hwkim3330/pi5-joycon-handheld/out/acrylic/v7_clear_acrylzip/preview_slot.png

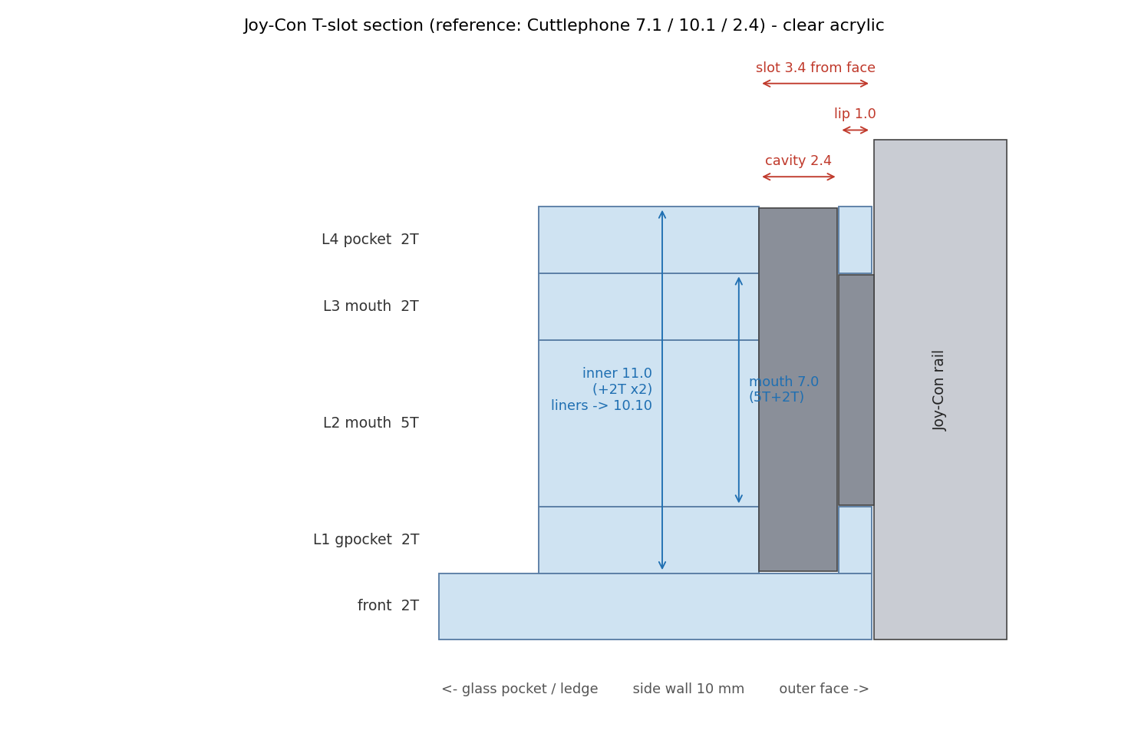
out/acrylic/v7_clear_acrylzip/preview_slot.png
