hwkim3330/pi5-joycon-handheld/out/acrylic/v8_clear_straightguide_ordered/sheet_2T.dxf

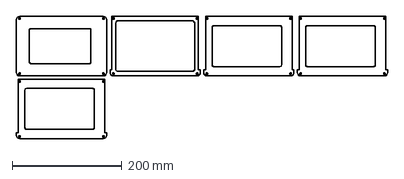
[picture p23: CAD file, 2026-09-11]
out/acrylic/v8_clear_straightguide_ordered/sheet_2T.dxf
675.6 x 222.9 mm
