hwkim3330/pi5-joycon-handheld/out/acrylic/v8r_liplayers_recut/L5r_pocket_lip_2T.dxf

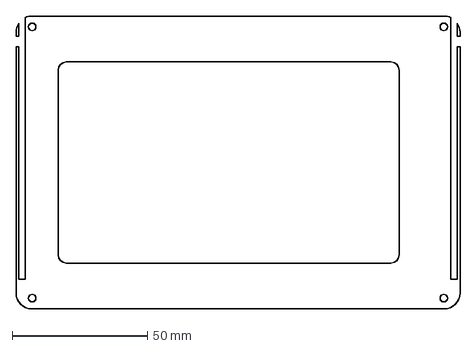
[picture p24: CAD file, 2026-09-11]
out/acrylic/v8r_liplayers_recut/L5r_pocket_lip_2T.dxf
164.4 x 108.5 mm
