hwkim3330/pi5-joycon-handheld/out/acrylic/test_coupon_exact/sheet_1.5T.dxf

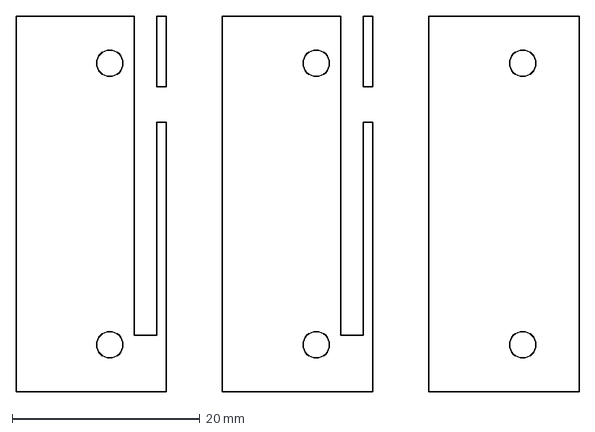
[picture p26: CAD file, 2026-09-11]
out/acrylic/test_coupon_exact/sheet_1.5T.dxf
60.0 x 40.0 mm
