hwkim3330/pi5-joycon-handheld/out/acrylic/v7_clear_acrylzip/sheet_2T.dxf

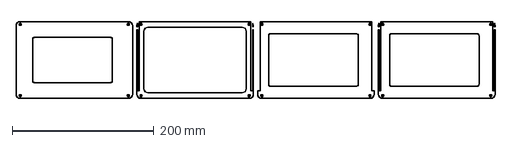
[picture p29: CAD file, 2026-09-11]
out/acrylic/v7_clear_acrylzip/sheet_2T.dxf
675.6 x 108.5 mm
