hwkim3330/pi5-joycon-handheld/out/acrylic/v8_clear_straightguide_ordered/L2_guide_3T.dxf

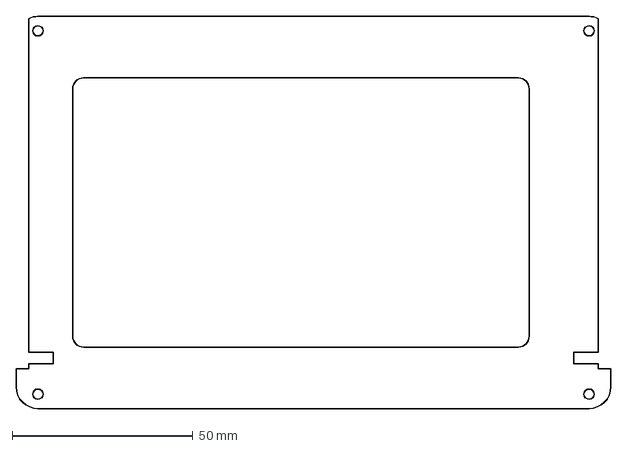
[picture p31: CAD file, 2026-09-11]
out/acrylic/v8_clear_straightguide_ordered/L2_guide_3T.dxf
164.4 x 108.5 mm
