hwkim3330/pi5-joycon-handheld/out/acrylic/test_coupon_acrylzip/sheet_2T.dxf

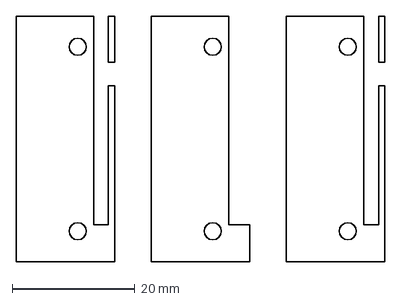
[picture p33: CAD file, 2026-09-11]
out/acrylic/test_coupon_acrylzip/sheet_2T.dxf
60.0 x 40.0 mm
