hwkim3330/pi5-joycon-handheld/out/acrylic/test_coupon_ordered/C2_guide_3T.dxf

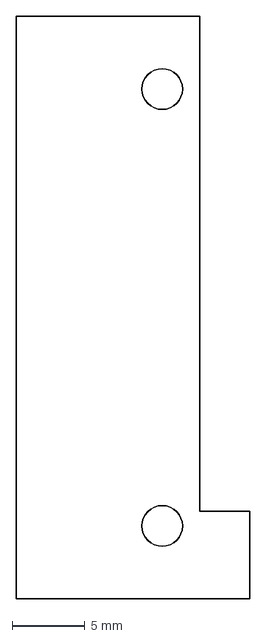
[picture p35: CAD file, 2026-09-11]
out/acrylic/test_coupon_ordered/C2_guide_3T.dxf
16.0 x 40.0 mm
