hwkim3330/pi5-joycon-handheld/out/acrylic/v4_open_back/sheet_3T.dxf

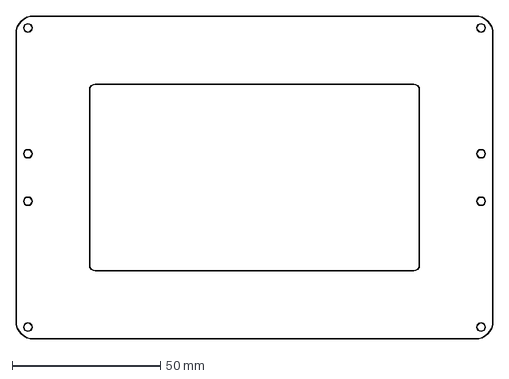
[picture p36: CAD file, 2026-09-08]
out/acrylic/v4_open_back/sheet_3T.dxf
161.0 x 109.0 mm
