hwkim3330/pi5-joycon-handheld/out/acrylic/v7_clear_exact/sheet_1.5T.dxf

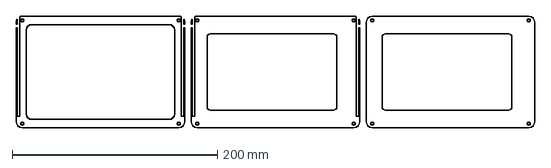
[picture p38: CAD file, 2026-09-11]
out/acrylic/v7_clear_exact/sheet_1.5T.dxf
505.2 x 108.5 mm
