hwkim3330/pi5-joycon-handheld/out/acrylic/test_coupon_exact/C4_pocket_1.5T.dxf

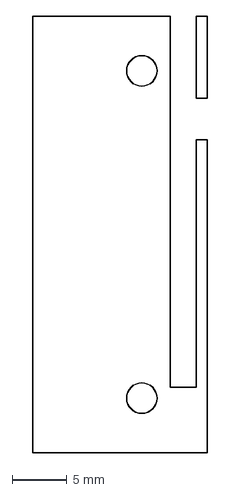
[picture p41: CAD file, 2026-09-11]
out/acrylic/test_coupon_exact/C4_pocket_1.5T.dxf
16.0 x 40.0 mm
