hwkim3330/pi5-joycon-handheld/out/acrylic/test_coupon_acrylzip/sheet_5T.dxf

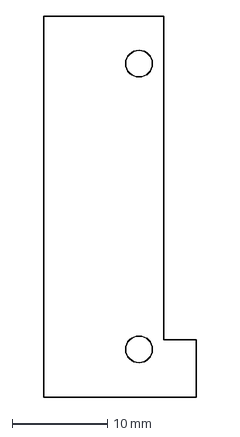
[picture p47: CAD file, 2026-09-11]
out/acrylic/test_coupon_acrylzip/sheet_5T.dxf
16.0 x 40.0 mm
