hwkim3330/pi5-joycon-handheld/out/acrylic/test_coupon_exact/C3_mouth_2T.dxf

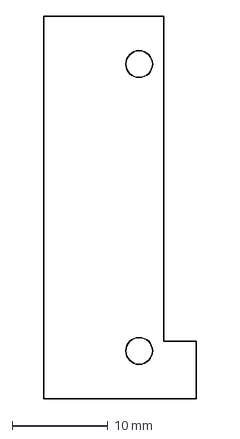
[picture p48: CAD file, 2026-09-11]
out/acrylic/test_coupon_exact/C3_mouth_2T.dxf
16.0 x 40.0 mm
