hwkim3330/pi5-joycon-handheld/out/acrylic/test_coupon_ordered/C4_guide_2T.dxf

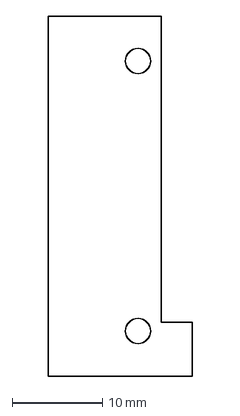
[picture p49: CAD file, 2026-09-11]
out/acrylic/test_coupon_ordered/C4_guide_2T.dxf
16.0 x 40.0 mm
