hwkim3330/pi5-joycon-handheld/out/acrylic/v7_clear_acrylzip/L1_gpocket_2T.dxf

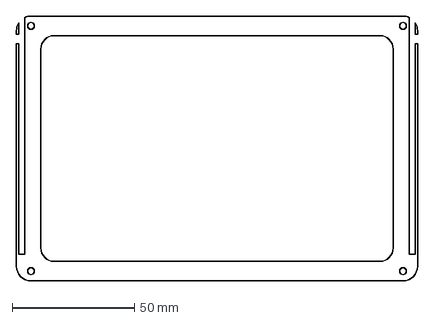
[picture p51: CAD file, 2026-09-11]
out/acrylic/v7_clear_acrylzip/L1_gpocket_2T.dxf
164.4 x 108.5 mm
