hwkim3330/pi5-joycon-handheld/out/acrylic/v8_clear_straightguide_ordered/L3_guide_2T.dxf

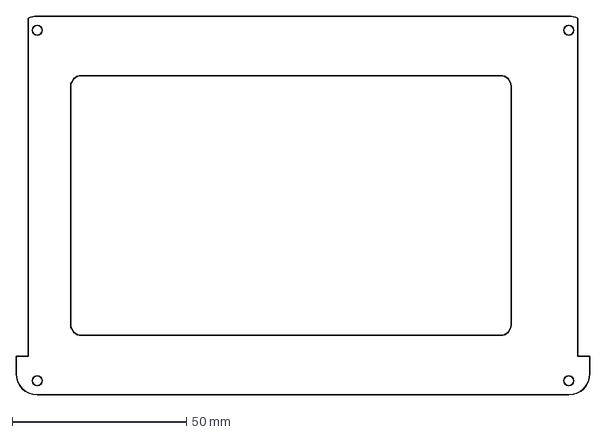
[picture p53: CAD file, 2026-09-11]
out/acrylic/v8_clear_straightguide_ordered/L3_guide_2T.dxf
164.4 x 108.5 mm
