hwkim3330/pi5-joycon-handheld/out/acrylic/test_coupon_ordered/stack_preview.stl

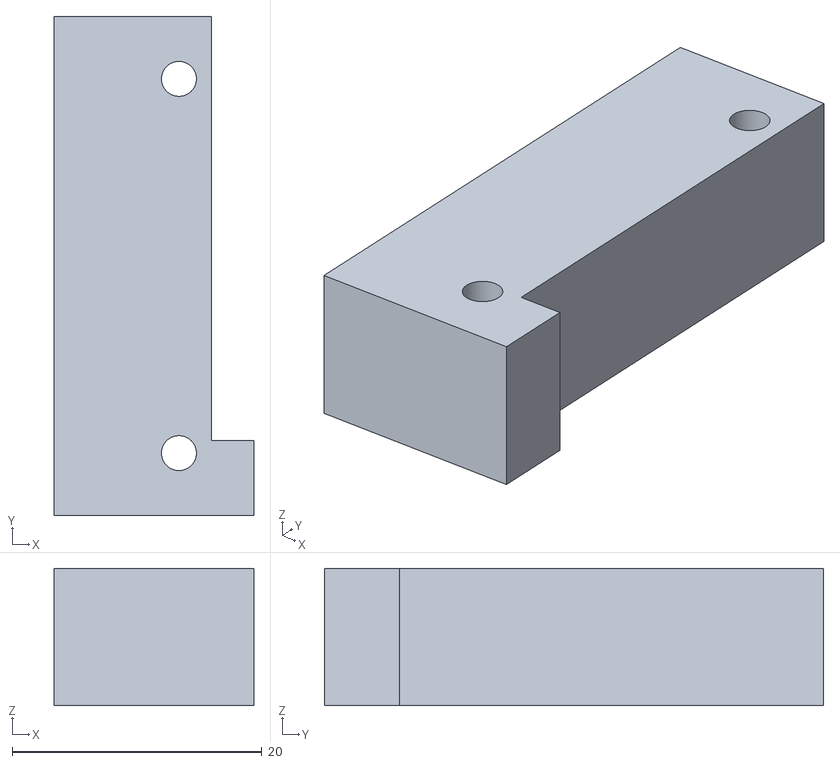
[picture p62: CAD file, 2026-09-11]
out/acrylic/test_coupon_ordered/stack_preview.stl
16.0 x 40.0 x 11.0
