hwkim3330/pi5-joycon-handheld/out/acrylic/v7_clear_acrylzip/stack_preview.stl

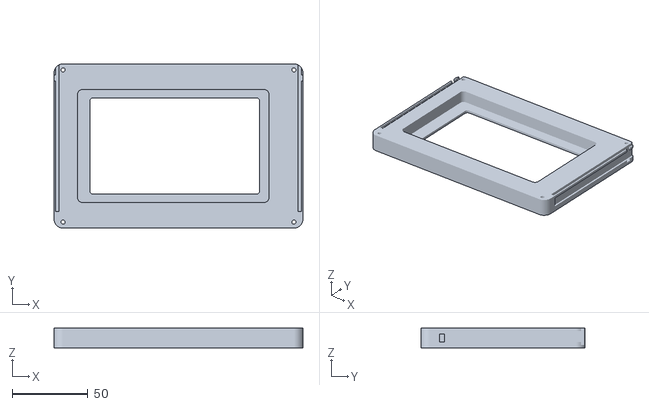
[picture p64: CAD file, 2026-09-08]
out/acrylic/v7_clear_acrylzip/stack_preview.stl
164.4 x 108.5 x 13.0
