hwkim3330/pi5-joycon-handheld/out/acrylic/v8_clear_straightguide_ordered/stack_preview.stl

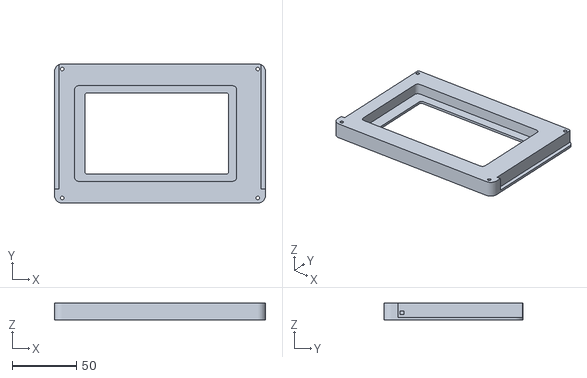
[picture p66: CAD file, 2026-09-11]
out/acrylic/v8_clear_straightguide_ordered/stack_preview.stl
164.4 x 108.5 x 13.0
