hwkim3330/pi5-joycon-handheld/out/acrylic/v7_clear_exact/L5_plain_1.5T.dxf

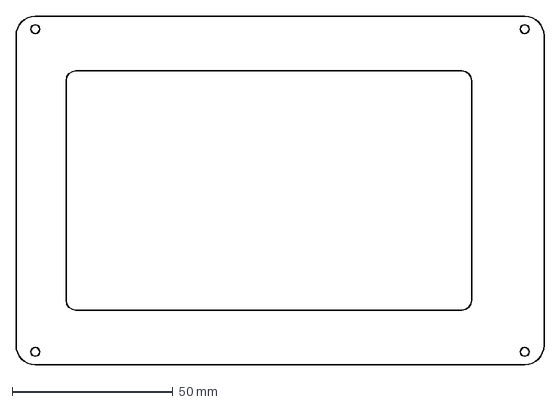
[picture p69: CAD file, 2026-09-11]
out/acrylic/v7_clear_exact/L5_plain_1.5T.dxf
164.4 x 108.5 mm
